prydin/toy-dac/fpga/toy-dac/src/sim/fifo_tb.v

`timescale 1ns / 1ps

// Testbench for the dual-clock fifo.v.
//
// Drives wr_clk and rd_clk at independent rates, with a deliberate
// frequency offset so the FIFO fill ramps in a known direction (the key
// behaviour the soft-PLL relies on).
//
// Scenarios:
//   1) Equal rates: fill stays roughly steady, no full / no empty,
//      no scoreboard mismatches.
//   2) Producer slightly faster than consumer: rd_count / wr_count
//      both rise over time but stay below DEPTH for the run length.
//   3) Producer slightly slower than consumer: counts fall toward 0.
//   4) Overrun: writes 100%, no reads → full asserts, count caps at
//      DEPTH, dropped writes counted.
//   5) Underrun: no writes, reads 100% → empty asserts, count stays 0,
//      noop reads counted.

module fifo_tb;

    localparam integer WIDTH         = 32;
    localparam integer DEPTH         = 16;       // power of 2
    localparam integer WR_PERIOD_NS  = 10;       // 100 MHz nominal
    localparam integer RD_PERIOD_NS  = 10;       // overridden per scenario

    reg wr_clk = 0;
    reg rd_clk = 0;
    integer wr_half = WR_PERIOD_NS/2;
    integer rd_half = RD_PERIOD_NS/2;

    always #(wr_half) wr_clk = ~wr_clk;
    always #(rd_half) rd_clk = ~rd_clk;

    reg                     wr_rst  = 1;
    reg                     rd_rst  = 1;

    reg                     wr_en   = 0;
    reg  signed [WIDTH-1:0] wr_data = 0;
    wire                    full;
    wire [$clog2(DEPTH+1)-1:0] wr_count;

    reg                     rd_en = 0;
    wire signed [WIDTH-1:0] rd_data;
    wire                    empty;
    wire [$clog2(DEPTH+1)-1:0] rd_count;

    fifo #(
        .WIDTH(WIDTH),
        .DEPTH(DEPTH)
    ) uut (
        .wr_clk   (wr_clk),
        .wr_rst   (wr_rst),
        .wr_data  (wr_data),
        .wr_en    (wr_en),
        .full     (full),
        .wr_count (wr_count),

        .rd_clk   (rd_clk),
        .rd_rst   (rd_rst),
        .rd_data  (rd_data),
        .rd_en    (rd_en),
        .empty    (empty),
        .rd_count (rd_count)
    );

    // ── Scoreboard: queue of expected read values ──
    integer expect_q [0:8191];
    integer expect_head = 0;
    integer expect_tail = 0;
    integer mismatches  = 0;

    // Push on every accepted write (wr_clk domain)
    integer next_data = 1;
    always @(posedge wr_clk) begin
        if (!wr_rst && wr_en && !full) begin
            expect_q[expect_tail] = next_data;
            expect_tail = expect_tail + 1;
            next_data   = next_data + 1;
        end
    end

    // Pop on every accepted read and compare (rd_clk domain)
    always @(posedge rd_clk) begin
        if (!rd_rst && rd_en && !empty) begin
            if (rd_data !== expect_q[expect_head]) begin
                $display("t=%0t  MISMATCH  got=%0d  expected=%0d  rd_count=%0d",
                         $time, rd_data, expect_q[expect_head], rd_count);
                mismatches = mismatches + 1;
            end
            expect_head = expect_head + 1;
        end
    end

    // ── Per-side monitors ──
    integer max_rd_count;
    integer min_rd_count_after_fill;
    integer full_seen;
    integer empty_seen;
    integer dropped_writes;
    integer noop_reads;

    always @(posedge wr_clk) if (!wr_rst) begin
        if (full)            full_seen      = full_seen + 1;
        if (wr_en && full)   dropped_writes = dropped_writes + 1;
    end
    always @(posedge rd_clk) if (!rd_rst) begin
        if (rd_count > max_rd_count) max_rd_count = rd_count;
        if (empty)           empty_seen = empty_seen + 1;
        if (rd_en && empty)  noop_reads = noop_reads + 1;
    end

    task reset_monitors;
        begin
            max_rd_count            = 0;
            min_rd_count_after_fill = DEPTH;
            full_seen               = 0;
            empty_seen              = 0;
            dropped_writes          = 0;
            noop_reads              = 0;
            mismatches              = 0;
        end
    endtask

    task do_reset;
        begin
            wr_en = 0; rd_en = 0; wr_data = 0;
            wr_rst = 1; rd_rst = 1;
            #100;
            @(negedge wr_clk); wr_rst = 0;
            @(negedge rd_clk); rd_rst = 0;
            #50;
            expect_head = 0;
            expect_tail = 0;
            next_data   = 1;
            reset_monitors;
        end
    endtask

    // Drive wr_en independently in its own clock domain
    integer wr_active = 0;
    integer wr_rate   = 0; // 0..100
    always @(negedge wr_clk) begin
        if (!wr_rst && wr_active) begin
            wr_en   <= ({$random} % 100) < wr_rate;
            wr_data <= next_data;   // value latched if accepted
        end else begin
            wr_en   <= 0;
        end
    end

    // Drive rd_en independently in its own clock domain
    integer rd_active = 0;
    integer rd_rate   = 0;
    always @(negedge rd_clk) begin
        if (!rd_rst && rd_active)
            rd_en <= ({$random} % 100) < rd_rate;
        else
            rd_en <= 0;
    end

    task run_for_ns(input integer ns);
        begin
            #ns;
        end
    endtask

    integer fails = 0;
    task check(input [255:0] name, input cond);
        begin
            if (cond) $display("  PASS: %0s", name);
            else begin $display("  FAIL: %0s", name); fails = fails + 1; end
        end
    endtask

    initial begin
        $display("=== fifo_tb (async, DEPTH=%0d) ===", DEPTH);

        // ── 1) Equal rates ────────────────────────────────────────────
        $display("\n--- Scenario 1: equal clocks, balanced 50%%/50%% ---");
        wr_half = 5; rd_half = 5;     // both 100 MHz
        do_reset;
        wr_rate = 50; rd_rate = 50;
        wr_active = 1; rd_active = 1;
        run_for_ns(20_000);
        wr_active = 0; rd_active = 0;
        run_for_ns(200);
        $display("  rd_count=%0d max_rd=%0d full=%0d empty=%0d mismatches=%0d",
                 rd_count, max_rd_count, full_seen, empty_seen, mismatches);
        // With random 50/50 traffic on a small FIFO the random walk will
        // briefly touch both rails — that's the FIFO doing its job, not a
        // bug. The only real invariant is no data corruption.
        check("no mismatches",                 mismatches == 0);

        // ── 2) Producer faster ────────────────────────────────────────
        $display("\n--- Scenario 2: wr_clk faster than rd_clk (10%%) ---");
        wr_half = 5;  rd_half = 6;    // rd ~ 83 MHz vs wr 100 MHz
        do_reset;
        wr_rate = 50; rd_rate = 50;
        wr_active = 1; rd_active = 1;
        run_for_ns(20_000);
        wr_active = 0; rd_active = 0;
        run_for_ns(200);
        $display("  rd_count=%0d max_rd=%0d full=%0d mismatches=%0d",
                 rd_count, max_rd_count, full_seen, mismatches);
        // With wr faster than rd, accumulated drift will reach DEPTH; the
        // FIFO is allowed to saturate at full and drop. What we require:
        // no out-of-order data, and the fill DID grow.
        check("no mismatches",                 mismatches == 0);
        check("rd_count grew above zero",      max_rd_count > 0);

        // ── 3) Producer slower ────────────────────────────────────────
        // Pre-fill to mid-depth, then drain with rd_clk faster than wr_clk.
        $display("\n--- Scenario 3: wr_clk slower than rd_clk (after pre-fill) ---");
        wr_half = 5; rd_half = 5;
        do_reset;
        wr_rate = 100; rd_rate = 0;
        wr_active = 1; rd_active = 1;
        run_for_ns(800);              // fill some
        reset_monitors;
        wr_half = 6; rd_half = 5;     // wr slower
        wr_rate = 50; rd_rate = 50;
        run_for_ns(20_000);
        wr_active = 0; rd_active = 0;
        run_for_ns(200);
        $display("  rd_count=%0d empty=%0d mismatches=%0d",
                 rd_count, empty_seen, mismatches);
        // Symmetric to scenario 2: drain-direction drift will reach 0.
        check("no mismatches",                 mismatches == 0);
        check("final rd_count below pre-fill", rd_count < DEPTH);

        // ── 4) Overrun ────────────────────────────────────────────────
        $display("\n--- Scenario 4: overrun (writes 100%%, reads 0%%) ---");
        wr_half = 5; rd_half = 5;
        do_reset;
        wr_rate = 100; rd_rate = 0;
        wr_active = 1; rd_active = 1;
        run_for_ns(5_000);
        wr_active = 0;
        run_for_ns(200);
        $display("  rd_count=%0d wr_count=%0d full=%0d dropped=%0d mismatches=%0d",
                 rd_count, wr_count, full_seen, dropped_writes, mismatches);
        check("full asserted",                 full_seen > 0);
        check("wr_count capped at DEPTH",      wr_count == DEPTH);
        check("at least one dropped write",    dropped_writes > 0);
        check("no mismatches on accepted data", mismatches == 0);

        // ── 5) Underrun ───────────────────────────────────────────────
        $display("\n--- Scenario 5: underrun (writes 0%%, reads 100%%) ---");
        do_reset;
        wr_rate = 0; rd_rate = 100;
        wr_active = 1; rd_active = 1;
        run_for_ns(5_000);
        rd_active = 0;
        run_for_ns(200);
        $display("  rd_count=%0d empty=%0d noop_reads=%0d mismatches=%0d",
                 rd_count, empty_seen, noop_reads, mismatches);
        check("empty asserted",                empty_seen > 0);
        check("rd_count stayed at 0",          max_rd_count == 0);
        check("at least one noop read",        noop_reads > 0);
        check("no spurious data delivered",    mismatches == 0);

        $display("\n=== Summary: %0s (%0d fails) ===",
                 (fails == 0) ? "ALL PASS" : "FAILURES", fails);
        $finish;
    end

endmodule
